filipe3x/proto-circadian-clock/product/COMMERCIALIZATION_STRATEGY.md

# Estratégia de Comercialização - Proto Circadian Clock

## Sumário Executivo

O **Proto Circadian Clock** é um dispositivo de iluminação inteligente que simula o ciclo solar natural para otimização do ritmo circadiano. Este documento apresenta uma estratégia completa para transformar este protótipo num produto comercial de massa.

---

## 1. Análise de Mercado

### 1.1 Tamanho do Mercado

| Segmento | Valor Global (2024) | Crescimento Anual |
|---|---|---|
| Dispositivos de Bem-Estar | $52.5B | 8.6% CAGR |
| Light Therapy Devices | $1.2B | 6.8% CAGR |
| Smart Home Lighting | $28.7B | 12.4% CAGR |
| Sleep Tech Market | $15.2B | 14.8% CAGR |

### 1.2 Público-Alvo

**Segmento Primário (Early Adopters):**
- Biohackers e entusiastas de wellness (25-45 anos)
- Trabalhadores remotos preocupados com saúde
- Pessoas com distúrbios de sono
- Utilizadores com SAD (Seasonal Affective Disorder)

**Segmento Secundário:**
- Trabalhadores por turnos (enfermeiros, seguranças, etc.)
- Viajantes frequentes (jet lag)
- Pais com bebés (estabelecer rotinas)
- Clínicas de sono e wellness

**Segmento Terciário (B2B):**
- Hotéis de luxo e spas
- Escritórios e espaços de coworking
- Hospitais e clínicas
- Escolas e universidades

### 1.3 Análise Competitiva

| Produto | Preço | Pontos Fortes | Pontos Fracos |
|---|---|---|---|
| Philips Wake-Up Light | €120-200 | Marca forte, qualidade | Apenas simulador de amanhecer |
| Lumie Bodyclock | €80-300 | Especializado, clínico | Design datado, caro |
| Hatch Restore | €130 | App, sons, moderno | Subscripção, dependente de WiFi |
| Circadian Optics | €50-80 | Acessível | Apenas luz estática |
| **Proto Circadian Clock** | €89-129 | Ciclo solar real, offline, open-source | Marca nova |

### 1.4 Proposta de Valor Única (UVP)

> **"O único dispositivo que replica o ciclo solar real da sua localização, ajustando automaticamente a temperatura de cor ao longo do dia - com ou sem internet."**

**Diferenciadores-chave:**
1. Cálculos astronómicos reais (não apenas timers)
2. Funciona 100% offline (RTC backup)
3. Open-source e customizável
4. Design minimalista com display LED visível
5. Preço competitivo

---

## 2. Análise de Custos e Pricing

### 2.1 Bill of Materials (BOM) - Custo por Unidade

| Componente | Custo Unitário (1k) | Custo Unitário (10k) | Custo Unitário (50k) |
|---|---|---|---|
| ESP32-WROOM-32D | €2.80 | €2.20 | €1.80 |
| Painel P10 32x16 RGB | €12.00 | €9.50 | €7.50 |
| RTC DS3231 | €1.50 | €1.10 | €0.85 |
| Bateria CR2032 | €0.30 | €0.20 | €0.15 |
| Botão + componentes | €0.50 | €0.35 | €0.25 |
| Fonte 5V 3A | €3.00 | €2.20 | €1.80 |
| PCB personalizada | €2.50 | €1.50 | €0.90 |
| Caixa/Enclosure | €4.00 | €2.80 | €2.00 |
| Cabos e conectores | €1.00 | €0.70 | €0.50 |
| **Total BOM** | **€27.60** | **€20.55** | **€15.75** |

### 2.2 Custos Adicionais por Unidade

| Item | 1k unidades | 10k unidades | 50k unidades |
|---|---|---|---|
| Montagem (SMT + manual) | €8.00 | €5.00 | €3.50 |
| Teste e QC | €2.00 | €1.20 | €0.80 |
| Embalagem | €3.00 | €2.00 | €1.50 |
| Certificações (amortizado) | €5.00 | €1.00 | €0.30 |
| Logística para armazém | €2.00 | €1.50 | €1.00 |
| **Total Adicional** | **€20.00** | **€10.70** | **€7.10** |

### 2.3 Custo Total de Produção

| Volume | Custo/Unidade | Investimento Total |
|---|---|---|
| 1,000 unidades | €47.60 | €47,600 |
| 10,000 unidades | €31.25 | €312,500 |
| 50,000 unidades | €22.85 | €1,142,500 |

### 2.4 Estratégia de Pricing

**Modelo de Pricing Tiered:**

| Modelo | Preço Sugerido | Margem (10k vol) | Target |
|---|---|---|---|
| **Circadian Mini** (sem RTC) | €69.00 | 55% | Entry-level |
| **Circadian Standard** | €99.00 | 68% | Mainstream |
| **Circadian Pro** (+ sensores) | €149.00 | 72% | Enthusiasts |
| **Circadian B2B** (bulk 10+) | €79.00/un | 60% | Empresas |

**Análise de Break-Even:**

| Cenário | Preço Médio | Custo | Margem | Break-even (custos fixos €50k) |
|---|---|---|---|---|
| Conservador | €89 | €31.25 | €57.75 | 866 unidades |
| Realista | €99 | €31.25 | €67.75 | 738 unidades |
| Otimista | €109 | €31.25 | €77.75 | 643 unidades |

---

## 3. Projeção Financeira

### 3.1 Cenário de 3 Anos

| Métrica | Ano 1 | Ano 2 | Ano 3 |
|---|---|---|---|
| Unidades vendidas | 3,000 | 12,000 | 35,000 |
| Receita bruta | €297,000 | €1,188,000 | €3,465,000 |
| Custo de produção | €141,000 | €375,000 | €800,000 |
| Margem bruta | €156,000 | €813,000 | €2,665,000 |
| Marketing (20%) | €59,400 | €237,600 | €693,000 |
| Operações (15%) | €44,550 | €178,200 | €519,750 |
| **Lucro líquido** | **€52,050** | **€397,200** | **€1,452,250** |
| **Margem líquida** | **17.5%** | **33.4%** | **41.9%** |

### 3.2 Investimento Inicial Necessário

| Categoria | Valor |
|---|---|
| Desenvolvimento de produto (v2.0) | €15,000 |
| Certificações (CE, FCC, RoHS) | €8,000 |
| Tooling (moldes, PCB setup) | €12,000 |
| Stock inicial (1,000 un) | €48,000 |
| Marketing de lançamento | €15,000 |
| Website e e-commerce | €5,000 |
| Legal e IP | €4,000 |
| Contingência (15%) | €16,050 |
| **Total Investimento** | **€123,050** |

---

## 4. Parcerias Estratégicas

### 4.1 Parcerias de Produção

| Tipo | Parceiros Potenciais | Benefício | Prioridade |
|---|---|---|---|
| **OEM/ODM China** | Shenzhen manufacturers (Seeed, JLCPCB, Elecrow) | Custo baixo, escala | Alta |
| **EMS Portugal/EU** | Arquiled, Inovaworks, Tekever | Proximidade, "Made in EU" | Média |
| **PCB Assembly** | JLCPCB, PCBWay, AllPCB | PCB + SMT integrado | Alta |
| **Enclosure** | Fictiv, Protolabs, Xometry | Prototipagem rápida | Média |

**Recomendação:** Começar com JLCPCB/Seeed para volumes iniciais (1-10k), migrar para EMS europeia quando viável economicamente para branding "Made in EU".

### 4.2 Parcerias de Distribuição

| Canal | Parceiros | Comissão | Potencial |
|---|---|---|---|
| **Amazon EU/US** | Seller Central, FBA | 15-20% | Muito Alto |
| **Wellness Marketplaces** | Goop, Thrive Market | 25-30% | Alto |
| **Tech/Gadget** | Uncrate, Touch of Modern | 30-40% | Médio-Alto |
| **Retail Electronics** | Fnac, MediaMarkt, Saturn | 35-45% | Alto |
| **Home Automation** | Home Assistant Store, SmartThings | 20-25% | Médio |
| **Kickstarter/Indiegogo** | Crowdfunding | 8-10% | Lançamento |

### 4.3 Parcerias de Co-Branding/Licenciamento

| Setor | Empresas Target | Modelo | Potencial de Receita |
|---|---|---|---|
| **Colchões/Sono** | Emma, Casper, Tempur | White-label, bundle | €200-500k/ano |
| **Smart Home** | Philips Hue, IKEA Tradfri | Integração, licença | €100-300k/ano |
| **Wellness Apps** | Calm, Headspace, Oura | Bundle digital | €50-150k/ano |
| **Hospitais/Clínicas** | CUF, Luz Saúde | B2B exclusivo | €150-400k/ano |
| **Hotéis** | Marriott, Hilton, NH | Piloto, rollout | €300k-1M/ano |

### 4.4 Parcerias Científicas/Credibilidade

| Instituição | Tipo de Parceria | Benefício |
|---|---|---|
| Universidades (Porto, Lisboa, Coimbra) | Estudos clínicos | Validação científica |
| Instituto do Sono | Endorsement | Credibilidade médica |
| Sleep Foundation (US) | Certificação | Acesso mercado US |
| Chronobiology International | Publicações | Autoridade científica |

### 4.5 Parcerias Tecnológicas

| Área | Parceiros | Objetivo |
|---|---|---|
| **IoT Platform** | Tuya, ESP RainMaker | App móvel white-label |
| **Voice Assistants** | Amazon Alexa, Google Home | Integração de voz |
| **Home Automation** | Home Assistant, MQTT | Comunidade open-source |
| **Health Platforms** | Apple Health, Google Fit | Tracking de sono |

### 4.6 Parcerias com Wearables

| Empresa | API Disponível | Dados Relevantes | Fit Estratégico |
|---|---|---|---|
| **WHOOP** | [Developer API](https://developer.whoop.com/) | Recovery Score, Sleep, HRV, Strain | ⭐⭐⭐⭐⭐ |
| **Oura Ring** | Sim | Sleep Score, Readiness, HRV | ⭐⭐⭐⭐⭐ |
| **Eight Sleep** | Sim | Temperatura, fases de sono | ⭐⭐⭐⭐⭐ |
| **Garmin** | Connect IQ | Body Battery, Sleep, Stress | ⭐⭐⭐⭐ |
| **Fitbit/Google** | Web API | Sleep Stages, SpO2 | ⭐⭐⭐ |
| **Apple Watch** | HealthKit (limitada) | Sleep, HRV | ⭐⭐⭐ |

**Integração WHOOP - Modelo Proposto:**
```
WHOOP API → App Circadian Clock → Ajuste automático de luz

Lógica:
- Recovery Score < 33% (red zone) → Luz quente 1h mais cedo
- Recovery Score 33-66% (yellow) → Ciclo solar normal
- Recovery Score > 66% (green) → Pode estender ciclo
- Sleep Consistency baixa → Ajuste gradual do offset
- HRV indica stress → Ativa red therapy mais cedo
```

**Potencial de Receita:**
| Modelo | Descrição | Receita Estimada |
|---|---|---|
| Bundle WHOOP + Circadian | Desconto cruzado, co-marketing | €100-200k/ano |
| White-label para WHOOP | "WHOOP Light" branded | €500k-2M (deal) |
| Integração premium | Feature paga na app | €50-100k/ano |

### 4.7 Parcerias com Biohackers e Influencers

**Influenciadores-Chave:**

| Nome | Plataforma | Audiência | Relevância | Custo Estimado |
|---|---|---|---|---|
| **Andrew Huberman** | Podcast/YouTube | 5M+ | ⭐⭐⭐⭐⭐ | €20-50k/episódio |
| **Bryan Johnson** | YouTube/X | 1M+ | ⭐⭐⭐⭐⭐ | Produto + equity |
| **Peter Attia** | Podcast | 1M+ | ⭐⭐⭐⭐ | €10-30k/episódio |
| **Dave Asprey** | Podcast/YouTube | 2M+ | ⭐⭐⭐⭐ | €5-15k |
| **Ben Greenfield** | Podcast | 500k+ | ⭐⭐⭐⭐ | €3-8k |
| **Rhonda Patrick** | YouTube | 1M+ | ⭐⭐⭐ | €5-12k |

**Fit Natural com Huberman Lab:**
O protocolo de sono do Dr. Huberman já recomenda:
- ✅ Exposição a luz natural 30-60 min após acordar
- ✅ Evitar luzes brilhantes entre 22h-4h
- ✅ Light therapy lamps como substituto do sol
- ✅ Red light à noite para não suprimir melatonina

**O Circadian Clock automatiza todo este protocolo!**

**Comunidades Target:**

| Comunidade | Membros | Plataforma | Estratégia |
|---|---|---|---|
| r/Biohackers | 350k+ | Reddit | Posts, AMAs |
| r/QuantifiedSelf | 100k+ | Reddit | Case studies |
| r/Nootropics | 300k+ | Reddit | Discussões sono |
| r/circadianrhythm | 15k+ | Reddit | Nicho direto |
| Huberman Lab Discord | 100k+ | Discord | Comunidade |
| Biohacker Center | 50k+ | Forum | Reviews |

**Estratégia de Influencer Marketing:**

| Fase | Ação | Investimento | ROI Esperado |
|---|---|---|---|
| 1. Seeding | 20 micro-influencers (5-50k) | €2,000 (produto) | 10-25x |
| 2. Reviews | 5 mid-tier (50-200k) | €5,000 | 8-15x |
| 3. Sponsors | 2 podcasts médios | €3,000 | 5-12x |
| 4. Major | Huberman/Attia pitch | €20-50k | 4-20x |

### 4.8 Parcerias com Atletas e Equipas Desportivas

**Referências de Mercado:**

| Empresa | Atletas/Equipas Parceiros | Modelo |
|---|---|---|
| **Eight Sleep** | Charles Leclerc (F1), Aaron Judge (MLB), Jimmy Butler (NBA), EF Pro Cycling | Ambassadors + Investors |
| **WHOOP** | Notre Dame Athletics, LeBron James, Michael Phelps, Patrick Mahomes | Team + Individual |
| **Dreams UK** | Team GB (Paris 2024) | Official Sleep Partner |

**Proposta de Valor para Atletas:**

| Problema do Atleta | Solução Circadian Clock |
|---|---|
| Viagens constantes (jet lag) | Ajuste automático de timezone |
| Treinos de madrugada | Dawn simulation adaptativo |
| Recuperação pós-competição | Red therapy mode intensivo |
| Quartos de hotel escuros | Portabilidade + funciona offline |
| Dados fragmentados | Integração com WHOOP/Oura/Garmin |

**Atletas/Equipas Target - Portugal:**

| Atleta/Equipa | Desporto | Fit | Potencial |
|---|---|-----|---|
| Cristiano Ronaldo | Futebol | ⭐⭐⭐⭐⭐ | Já é investidor WHOOP |
| Sporting/Benfica/Porto | Futebol | ⭐⭐⭐⭐ | Departamento médico |
| João Almeida | Ciclismo | ⭐⭐⭐⭐ | Grand Tours = jet lag |
| Miguel Oliveira | MotoGP | ⭐⭐⭐⭐ | Viagens constantes |
| Patrícia Mamona | Atletismo | ⭐⭐⭐ | Imagem wellness |
| Federação Portuguesa | Olímpicos | ⭐⭐⭐⭐ | LA 2028 prep |

**Atletas/Equipas Target - Internacional:**

| Segmento | Exemplos | Abordagem |
|---|---|---|
| Ciclistas WorldTour | UAE, Ineos, Jumbo | Recovery em Grand Tours |
| Pilotos F1/MotoGP | Via managers | Jet lag constante |
| NBA/NFL players | Via agências (CAA, WME) | Premium market |
| Tenistas | Via ATP/WTA | Circuito global |
| Atletas Olímpicos | Comités nacionais | Paris 2024 → LA 2028 |

**Modelos de Parceria Desportiva:**

| Modelo | Descrição | Investimento | Retorno |
|---|---|---|---|
| **Product Seeding** | Enviar a 50 atletas | €5,000 | Social proof |
| **Athlete Ambassador** | Atleta usa e promove | Produto + €1-5k/mês | Credibilidade |
| **Team Partnership** | Fornecedor oficial equipa | €10-50k/época | B2B + visibilidade |
| **Athlete Investor** | Equity por promoção | 1-5% equity | Compromisso longo |
| **Performance Study** | Estudo científico com equipa | €5-10k | Dados + PR |
| **Co-branded Edition** | "Circadian x [Atleta]" | Revenue share | Premium pricing |

**Plano de Ação - Atletas e Biohackers:**

| Semana | Ação |
|---|---|
| 1-2 | Produzir 50 unidades "beta tester edition" |
| 3-4 | Enviar a 20 micro-influencers biohacking |
| 5-6 | Contactar 5 atletas portugueses via Instagram/agentes |
| 7-8 | Criar landing page "Used by athletes & biohackers" |
| 9-12 | Recolher testemunhos e case studies |
| 13-16 | Aplicar a podcasts como sponsor |
| 17-20 | Pitch a equipas desportivas portuguesas |
| 21-24 | Lançar affiliate program (15% comissão) |

**ROI Estimado por Canal:**

| Canal | Investimento | Vendas Esperadas | ROI |
|---|---|---|-----|
| Micro-influencers (20x) | €2,000 | 200-500 unidades | 10-25x |
| Podcast pequeno | €1,000 | 50-150 unidades | 5-15x |
| Atleta português | €500 + produto | 100-300 unidades | 20-60x |
| Equipa de futebol | €15,000 | 500-1,500 unidades | 3-10x |
| Huberman mention | €30,000 | 2,000-10,000 unidades | 7-33x |

---

## 5. Estratégia de Go-to-Market

### 5.1 Fase 1: Validação (Meses 1-3)

**Objetivos:**
- Validar product-market fit
- Gerar buzz inicial
- Financiar produção inicial

**Ações:**
1. **Crowdfunding Campaign**
   - Plataforma: Kickstarter (maior audiência) ou Indiegogo (mais flexível)
   - Meta: €50,000 (1,000 unidades @ early bird €49)
   - Stretch goals: app móvel, sensores adicionais

2. **Community Building**
   - Subreddit r/biohackers, r/circadianrhythm
   - Fóruns: Quantified Self, Biohacker.center
   - Discord server para early adopters

3. **Content Marketing**
   - Blog posts sobre ciência circadiana
   - YouTube: build logs, behind-the-scenes
   - Podcast appearances (Huberman Lab pitch, etc.)

### 5.2 Fase 2: Lançamento (Meses 4-8)

**Canais de Venda:**

| Canal | Prioridade | Setup Time | Custo |
|---|---|---|---|
| Website próprio (Shopify) | Alta | 2 semanas | €300/mês |
| Amazon EU | Alta | 4-6 semanas | FBA fees |
| Amazon US | Média | 6-8 semanas | FBA fees |
| Etsy | Média | 1 semana | 6.5% |
| Retail (Fnac, etc.) | Baixa | 3-6 meses | Margem 40% |

**Marketing Mix:**

| Canal | Budget (%) | Objetivo |
|---|---|---|
| Meta Ads (FB/IG) | 35% | Awareness, conversão |
| Google Ads | 25% | Intent-based |
| Influencer Marketing | 20% | Credibilidade, reach |
| PR/Media | 10% | Earned media |
| Content/SEO | 10% | Long-term organic |

### 5.3 Fase 3: Escala (Meses 9-24)

**Expansão de Produto:**
- Circadian Pro (sensores de luz ambiente, HR)
- Circadian Bedside (versão compacta)
- Circadian Panel (painel de parede maior)
- Subscription: personalized light profiles via app

**Expansão Geográfica:**
1. Portugal/Espanha (base)
2. UK, Alemanha, França (Ano 1)
3. EUA, Canadá (Ano 2)
4. Ásia (Japão, Coreia) (Ano 3)

---

## 6. Requisitos Legais e Certificações

### 6.1 Certificações Obrigatórias

| Certificação | Mercado | Custo | Tempo |
|---|---|---|---|
| CE Marking | Europa | €2,000-4,000 | 4-8 semanas |
| FCC Part 15 | EUA | €2,000-3,000 | 4-6 semanas |
| RoHS | Global | €500-1,000 | 2-4 semanas |
| WEEE | Europa | €200-500 | 2 semanas |
| UL (opcional) | EUA | €5,000-10,000 | 8-12 semanas |

### 6.2 Propriedade Intelectual

**Recomendações:**
1. **Trademark** do nome "Circadian Clock" ou alternativo (€500-1,000)
2. **Design Patent** para enclosure único (€2,000-5,000)
3. **Utility Patent** para algoritmo de mapeamento solar-cor (€8,000-15,000)
4. Manter código **open-source** para hardware, proprietário para app/cloud

### 6.3 Compliance

| Área | Requisito |
|---|---|
| GDPR | Se app coleta dados de utilizador |
| Product Liability | Seguro obrigatório EU (€500-1,500/ano) |
| Garantia | Mínimo 2 anos EU |
| Right to Repair | Documentação de reparação pública |

---

## 7. Roadmap de Produto

### 7.1 Versão 2.0 (Comercial) - MVP

**Hardware:**
- [ ] PCB integrada (ESP32 + RTC + conectores)
- [ ] Enclosure profissional (injection molding)
- [ ] Fonte de alimentação integrada
- [ ] Cabo USB-C para configuração

**Software:**
- [ ] Interface web de configuração (WiFi AP mode)
- [ ] OTA updates
- [ ] Firmware criptografado
- [ ] Factory reset físico

### 7.2 Versão 2.5 - Enhanced

**Adições:**
- [ ] App móvel (iOS/Android) via BLE
- [ ] Sensor de luz ambiente (auto-brightness)
- [ ] Alarme com dawn simulation
- [ ] Múltiplos perfis de utilizador

### 7.3 Versão 3.0 - Pro

**Adições:**
- [ ] Integração Home Assistant nativa
- [ ] Amazon Alexa / Google Home
- [ ] Sensor de presença
- [ ] Painel maior (64x32)
- [ ] Audio (white noise, alarmes)

---

## 8. Equipa Necessária

### 8.1 Fase Inicial (Fundador + Freelancers)

| Função | Tipo | Custo/Mês |
|---|---|---|
| Founder/Product | Full-time | €0 (equity) |
| Hardware Engineer | Freelance | €2,000-3,000 |
| Industrial Designer | Freelance | €1,500-2,500 |
| Marketing/Growth | Part-time | €1,000-1,500 |

### 8.2 Fase de Escala (Ano 2+)

| Função | Tipo | Prioridade |
|---|---|---|
| Operations Manager | Full-time | Alta |
| Software Developer (App) | Full-time | Alta |
| Customer Support | Part-time | Média |
| Sales (B2B) | Full-time | Média |

---

## 9. Riscos e Mitigações

| Risco | Probabilidade | Impacto | Mitigação |
|---|---|---|---|
| Competidor grande copia | Média | Alto | Patents, brand loyalty, features |
| Supply chain disruption | Média | Alto | Multiple suppliers, stock buffer |
| Certificação falha | Baixa | Alto | Pre-compliance testing |
| Adoção lenta | Média | Médio | Pivoting, B2B focus |
| Câmbio EUR/USD | Média | Baixo | Hedging, pricing dinâmico |

---

## 10. Próximos Passos Imediatos

### Semana 1-2
- [ ] Registar marca "Circadian Clock" ou alternativa
- [ ] Criar landing page com email signup
- [ ] Definir especificações finais v2.0
- [ ] Contactar 3-5 manufacturers para quotes

### Semana 3-4
- [ ] Encomendar protótipos de enclosure
- [ ] Iniciar processo de certificação CE
- [ ] Preparar campanha Kickstarter
- [ ] Criar conteúdo para redes sociais

### Mês 2
- [ ] Finalizar design industrial
- [ ] Submeter para certificações
- [ ] Lançar pré-campanha Kickstarter
- [ ] Outreach a influencers

### Mês 3
- [ ] Lançar Kickstarter
- [ ] Confirmar parceiro de produção
- [ ] Desenvolver app MVP
- [ ] Estabelecer customer support

---

## 11. Contactos Úteis

### Fabricantes Recomendados
- **Seeed Studio** (Shenzhen): seeedstudio.com - Fusão de PCB/assembly
- **JLCPCB**: jlcpcb.com - PCB + SMT económico
- **Elecrow**: elecrow.com - Produção pequena escala
- **Arquiled** (Portugal): arquiled.pt - Made in Portugal

### Laboratórios de Certificação
- **TÜV Rheinland** (EU): tuv.com
- **Bureau Veritas** (Global): bureauveritas.com
- **Intertek** (FCC/UL): intertek.com

### Plataformas de Crowdfunding
- **Kickstarter**: kickstarter.com
- **Indiegogo**: indiegogo.com
- **Crowd Supply** (hardware focus): crowdsupply.com

---

## Conclusão

O Proto Circadian Clock tem potencial significativo num mercado em crescimento. Com um investimento inicial de ~€125k, é possível atingir break-even em menos de 1,000 unidades e gerar lucros substanciais a partir do Ano 2.

**Fatores críticos de sucesso:**
1. Qualidade de produto impecável
2. Certificações e compliance desde o início
3. Parcerias estratégicas (especialmente B2B)
4. Marketing focado em wellness/biohacking
5. Comunidade open-source ativa

**Potencial de exit (5 anos):**
- Aquisição por empresa de smart home: €5-15M
- Licenciamento de tecnologia: €2-5M/ano
- IPO (improvável mas possível): €20M+

---

*Documento criado: Dezembro 2024*
*Última atualização: Dezembro 2024*
*Versão: 1.1*
*Changelog: Adicionadas secções 4.6-4.8 (Wearables, Biohackers, Atletas)*
