filipe3x/proto-circadian-clock/product/hub75 pin correct position.pdf

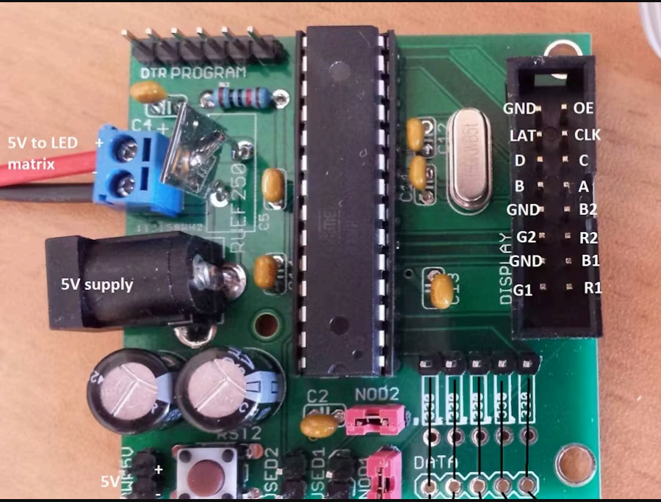
[picture p3: figure]
